alexnathanson/CASE_sensor_network/rpi_zero_sensor/airtable.py

import datetime
import json
import asyncio
import logging
import requests
from typing import Any, Dict, Optional, List

# ------------------ Airtable Class ------------------ #
class Airtable():
    def __init__(self, key:str, table:str, name:str=''):
        self.key = key
        self.url = 'https://api.airtable.com/v0/appWyfKF1xclZ6OtH/'
        self.table = table
        #self.IDs = []
        self.names=[]
        self.sensors={}

    # retrieves record IDs by name
    async def getRecordID(self,name:List)-> List:
        #IDlist = []
        for n in name:
            logging.debug(name)

            if self.sensors[n]['id']=='':
                try:
                    # get list of records filtered by name

                    mURL = f'{self.url}{self.table}?maxRecords=3&view=Grid%20view&filterByFormula=name%3D%22{n}%22' #filter results by name column
                    res = await self.send_secure_get_request(mURL)

                    logging.debug(res)

                    # pull the id for the first record
                    recordID = res['records'][0]['id']
                    #IDlist.append(recordID)
                    self.sensors[n]['id']=recordID

                    logging.debug(recordID)
                except Exception as e:
                    logging.error(e)

        #return IDlistDict

    # updates up to 10 records at once
    # https://airtable.com/developers/web/api/update-multiple-records
    async def updateBatch(self, names:List, sensors:List):

        # if (len(names) != len(data)) or (len(names) != len(recordIDs)):
        #     logging.error('length mismatch! :(')
        #     logging.error(recordIDs)
        #     logging.error(data)
        # logging.debug(names)
        # logging.debug(recordIDs)
        # logging.debug(data)

        records = []
        for n in names:
            if sensors[n]['data']=={}:
                continue

            #try:
            logging.debug(f'{n}!')

            # patch record - columns not included are not changed
            # keys in data must be identical to Airtable columns

            try:
                rec = {
                    "id": str(sensors[n]['id']),
                    "fields": {
                        "deviceName": str(n),
                        **{key: str(value) for key, value in sensors[n]['data'].items()}
                        }
                    }
            except Exception as e:
                logging.error(f'Exception while formatting sensor data: {e}')
                continue

            records.append(rec)
            # except Exception as e:
            #     logging.error(f'Exception while formatting sensor data: {e}')

        pData={"records": records}
        logging.debug(pData)

        try:

            patch_status = 0
            while patch_status < 3:
                # note that patch leaves unchanged data in place, while a post would delete old data in the record even if not being updated
                r = await self.send_patch_request(f'{self.url}{self.table}',pData)
                if r != False:
                    break
                await asyncio.sleep(1+patch_status)
                patch_status += 1
            logging.debug(r)
        except Exception as e:
            logging.error(f'Exception while patching Airtable: {e}')

    async def send_secure_get_request(self, url:str,type:str='json',timeout=2) -> Any:
        """Send GET request to the IP."""
        max_tries = 3

        headers = {"Content-Type": "application/json; charset=utf-8"}

        if self.key != '':
            headers = {"Authorization": f"Bearer {self.key}"}

        for attempt in range(max_tries):
            try:
                response = requests.get(url, headers=headers, timeout=timeout)
                response.raise_for_status()

                if type == 'json':
                    return response.json()
                elif type == 'text':
                    return (response.text, response.status_code)
                else:
                    return response.status_code
            except Exception as e:
                logging.error(f'{e}')
                if attempt == max_tries-1: # try up to 3 times
                    logging.debug('FAILED!!!')
                    return False
                else:
                    logging.debug('SLEEEEEEEEEEEEEEEEEPING')
                    await asyncio.sleep(3* int(attempt))

    async def send_patch_request(self, url:str, data:Dict={},timeout=1):

        headers = {"Content-Type": "application/json; charset=utf-8"}

        if self.key != '':
            headers = {"Content-Type": "application/json; charset=utf-8",
                "Authorization": f"Bearer {self.key}"}

        response = requests.patch(url, headers=headers, json=data)

        if response.ok:
            return response.json()
        else:
            logging.warning(f'{response.status_code}: {response.text}')
            return False
