alexnathanson/CASE_sensor_network/rpi_zero_sensor/examples/kasa_example_maybe_depreciated.py

# TP Link Kasa Smart Plug with Energy Monitoring
'''
documentation:
https://python-kasa.readthedocs.io/en/latest/index.html
https://python-kasa.readthedocs.io/en/latest/smartdevice.html
'''

import asyncio
from kasa import Discover, Credentials, Module
#from kasa.iot import IotPlug
from dotenv import load_dotenv
import os

load_dotenv()
un = os.getenv('KASA_UN')
pw = os.getenv('KASA_PW')

async def initialize():
    #discover a single specific device
    # device = await Discover.discover_single(
    #     "127.0.0.1",
    #     credentials=Credentials("myusername", "mypassword"),
    #     discovery_timeout=10
    # )


    devices = await Discover.discover(
        credentials=Credentials(un, pw),
        discovery_timeout=10
    )
    for ip, device in devices.items():
        await device.update()
        print(device.features)
        for feature_id, feature in device.features.items():
            print(f"{feature.name} ({feature_id}): {feature.value}")

  


    return devices

# get power and energy data
async def getData(dev):
    try:
        await dev.update()
        print('')
        print(f'{dev.features['current_consumption'].value} W')
        print(f'{dev.features['voltage'].value} V')
        print(f'{dev.features['current'].value} A')
        # w = float(dev.features.current) * float(dev.features.voltage)
        # print(f'{w} W')
        print("Outlet is on: " + str(dev.is_on))
        print('')
    # except Exception as e:
    #     print(e)
    finally:
        if hasattr(dev, "session"):
            await dev.session.close()

# flip state of outlet
async def flipState(dev):

    #p = SmartPlug(ip)
    await dev.update()

    if dev.is_on:
        print(dev.alias + ' is on. Turning off now...')
        await dev.turn_off()
    else:
        print(dev.alias + ' is off. Turning on now...')
        await dev.turn_on()

async def main():

    try:
        deviceList = await initialize()

        for ip, device in deviceList.items():
            #await flipState(device)
            await getData(device)
    except Exception as e:
        print(e)

if __name__ == "__main__":
    asyncio.run(main())


# # TP Link Kasa Smart Plug with Energy Monitoring
# '''
# documentation:
# https://python-kasa.readthedocs.io/en/latest/index.html
# https://python-kasa.readthedocs.io/en/latest/smartdevice.html
# '''

# import asyncio
# from kasa import Discover, Credentials, Module
# from kasa.iot import IotPlug

# async def initialize():
# 	#discover a single specific device
#     # device = await Discover.discover_single(
#     #     "127.0.0.1",
#     #     credentials=Credentials("myusername", "mypassword"),
#     #     discovery_timeout=10
#     # )

#     # await device.update()  # Request the update
#     # print(device.alias)  # Print out the alias

#     #discover all available devices
#     devices = await Discover.discover(
#         credentials=Credentials("myusername", "mypassword"),
#         discovery_timeout=10
#     )
#     for ip, device in devices.items():
#         await device.update()
#         print(device.alias + " ip: " + device.host)

#     return devices

# # get power and energy data
# async def getData(ip):
# 	p = IotPlug(ip)

# 	await p.update()
# 	energy = p.modules[Module.Energy]
# 	print(str(energy.status.power) + "W")
# 	print(str(energy.status.voltage) + "V")
# 	print(str(energy.status.current) + "I")
# 	print("Outlet is on: " + str(p.is_on))
# 	print(energy.data)

# # flip state of outlet
# async def flipState(ip):

# 	p = SmartPlug(ip)
# 	await p.update()

# 	if p.is_on:
# 		print(p.alias + ' is on. Turning off now...')
# 		await p.turn_off()
# 	else:
# 		print(p.alias + ' is off. Turning on now...')
# 		await p.turn_on()

# async def main():
# 	deviceList = await initialize()

# 	for ip, device in deviceList.items():
# 		#flip = await flipState(ip)
# 		await getData(ip)

# if __name__ == "__main__":
#     asyncio.run(main())
